KubbyDev/MusicBox/Modules/StepperMotors/Tests/FinalStepperControl/diagram.png

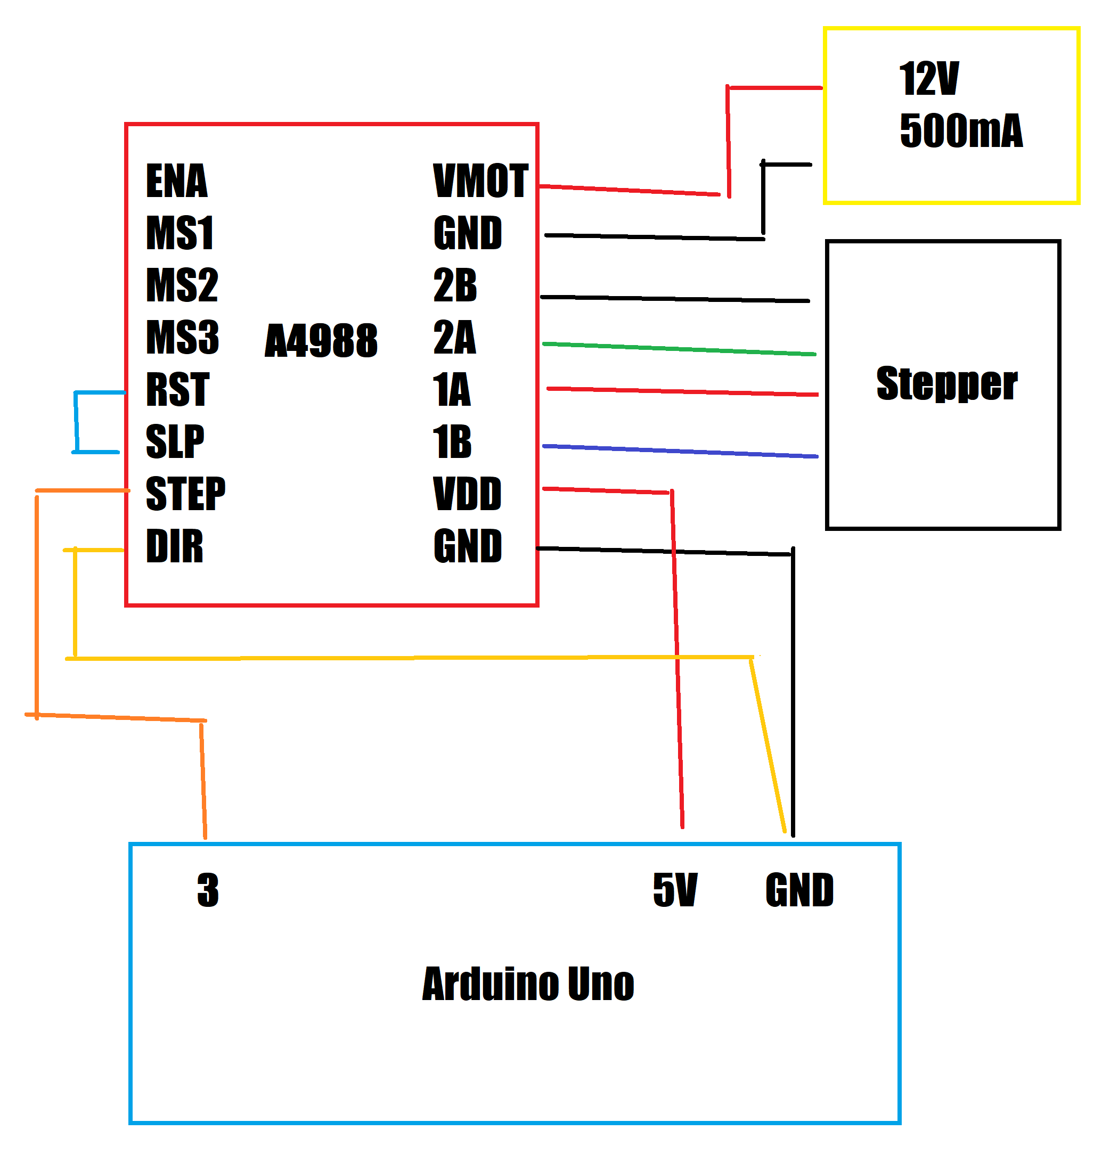
Modules/StepperMotors/Tests/FinalStepperControl/diagram.png
